ymkn/KeeBar/image/firmwaredownload.png

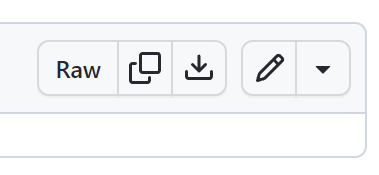
image/firmwaredownload.png
